xmotion-project/karaloop/src/karaloopP1_0.gif

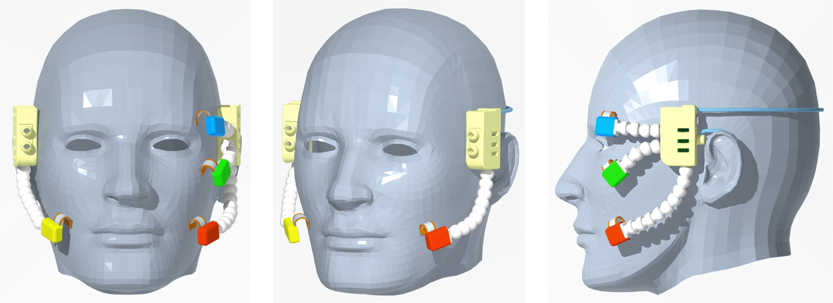
src/karaloopP1_0.gif
