xmotion-project/karaloop/src/karaloopP1_0_photo.gif

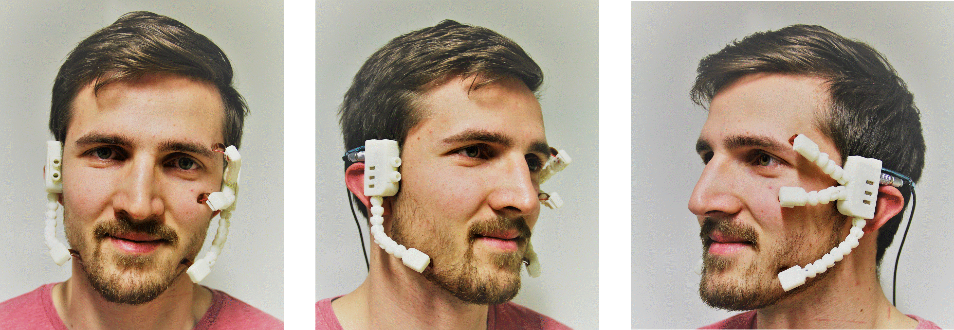
src/karaloopP1_0_photo.gif
