xmotion-project/karaloop/src/karaloopP2_0.gif

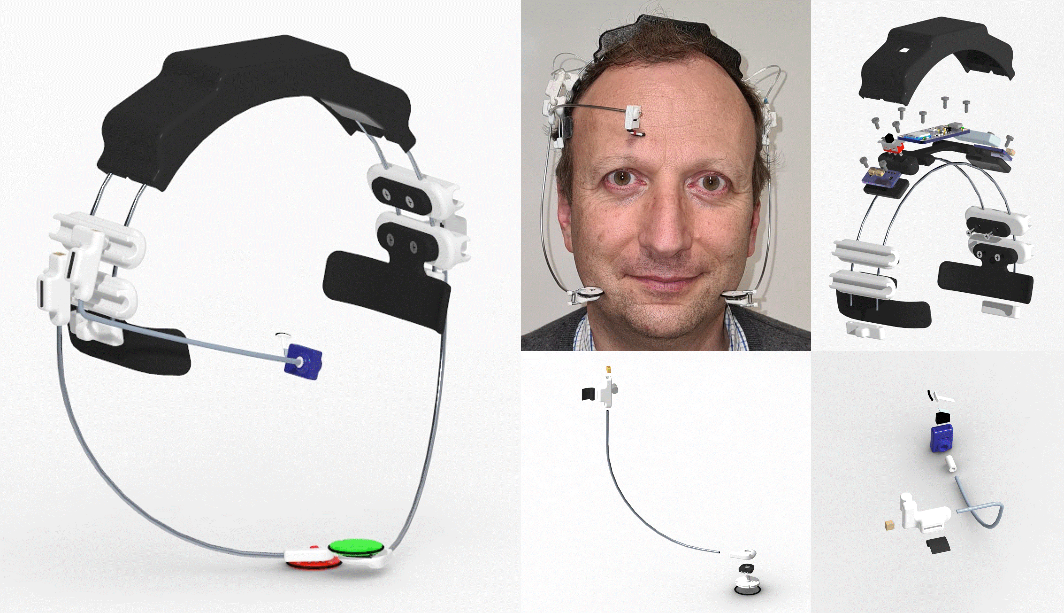
src/karaloopP2_0.gif
