xmotion-project/karaloop/src/karaloopP3_0.gif

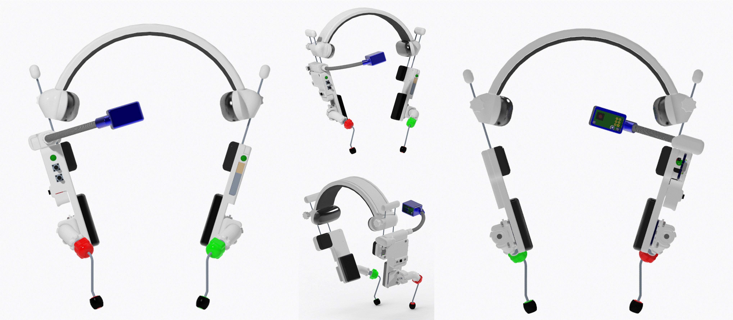
src/karaloopP3_0.gif
