xmotion-project/karaloop/src/ShortDemo_iMacWhatsapp.gif

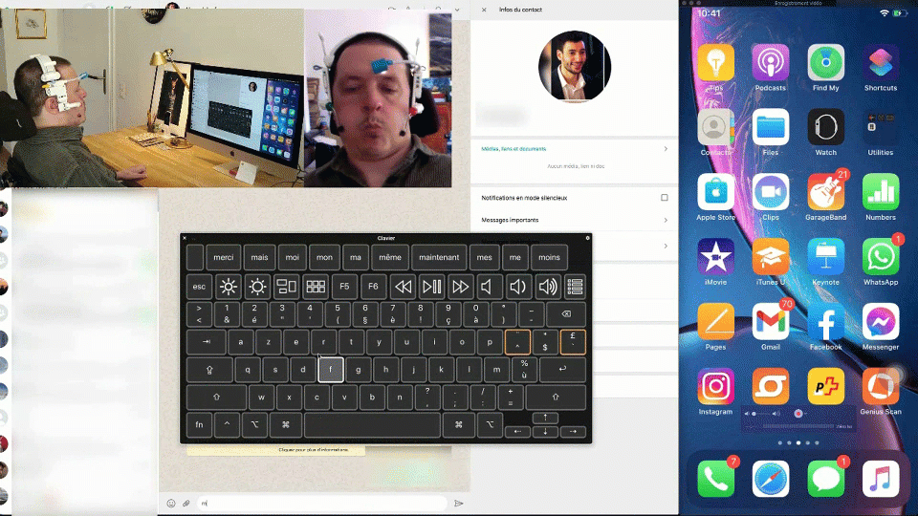
src/ShortDemo_iMacWhatsapp.gif
