xmotion-project/karaloop/src/karaloopP1_0_components.jpg

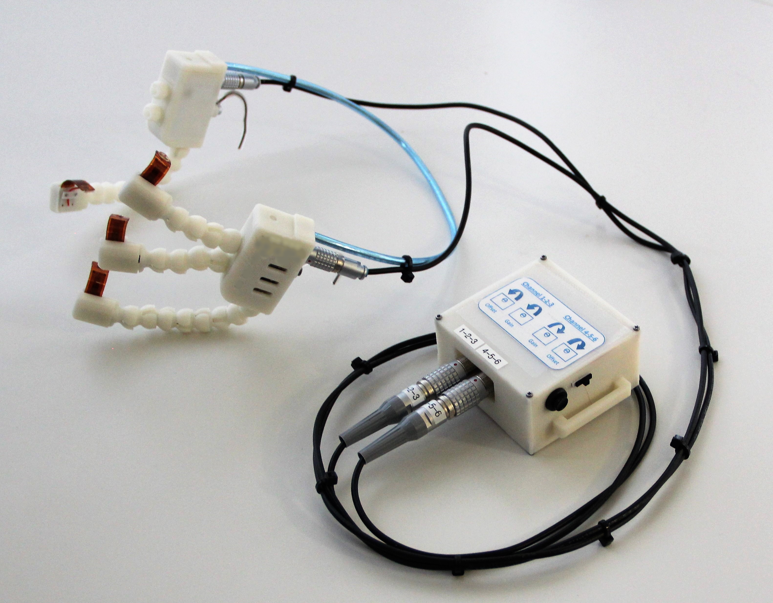
src/karaloopP1_0_components.jpg
