xmotion-project/karaloop/src/karaloopP1_0_parts.gif

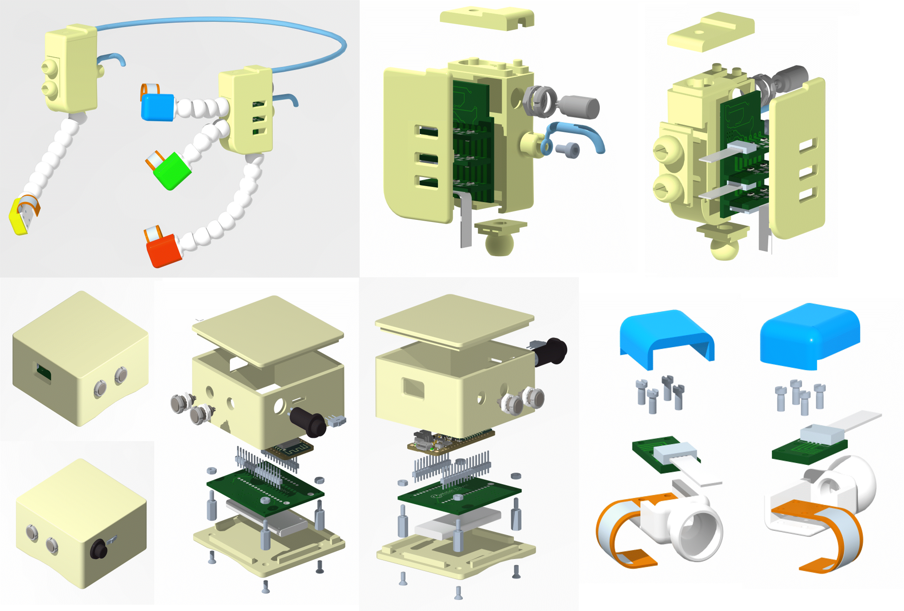
src/karaloopP1_0_parts.gif
