xmotion-project/karaloop/karaloop_P3_0/Hardware/Mechanical Design/Sub-assembly/Optical probe/STL/sliding_join_female.stl

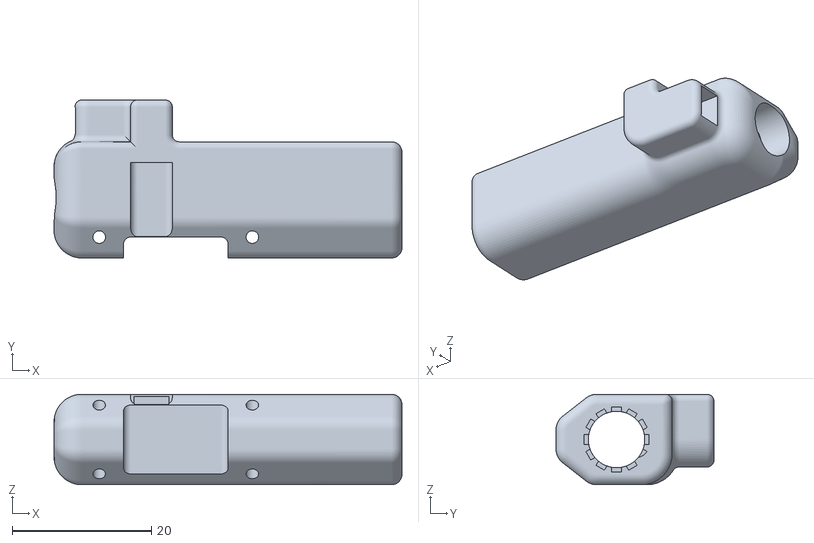
[picture p31: CAD file, 2021-08-26]
karaloop_P3_0/Hardware/Mechanical Design/Sub-assembly/Optical probe/STL/sliding_join_female.stl
50.0 x 22.7 x 13.0
