xmotion-project/karaloop/karaloop_P3_0/Hardware/Mechanical Design/Sub-assembly/Right hub/STL/hub_end_part.stl

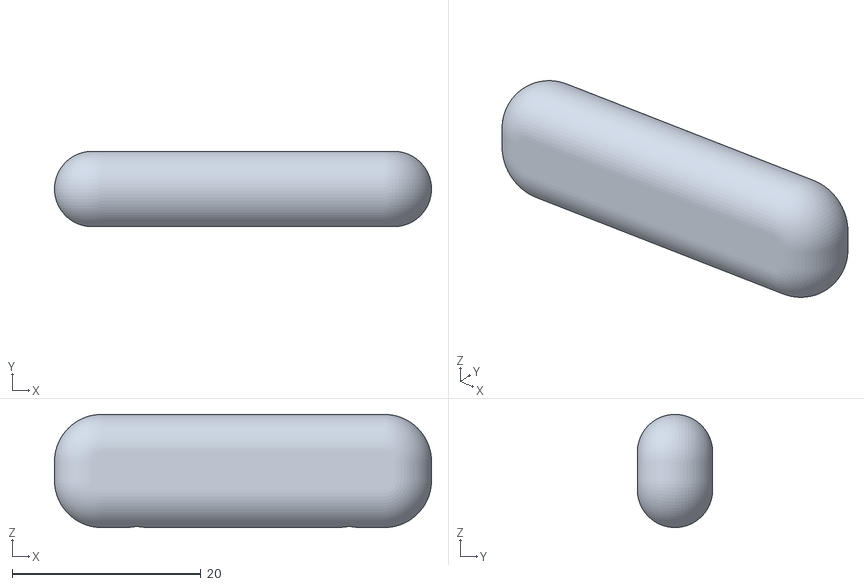
[picture p32: CAD file, 2021-08-26]
karaloop_P3_0/Hardware/Mechanical Design/Sub-assembly/Right hub/STL/hub_end_part.stl
40.0 x 8.00 x 12.0
