xmotion-project/karaloop/karaloop_P1_0/Hardware/Mechanical Design/STL/bottom_cover_control_box.stl

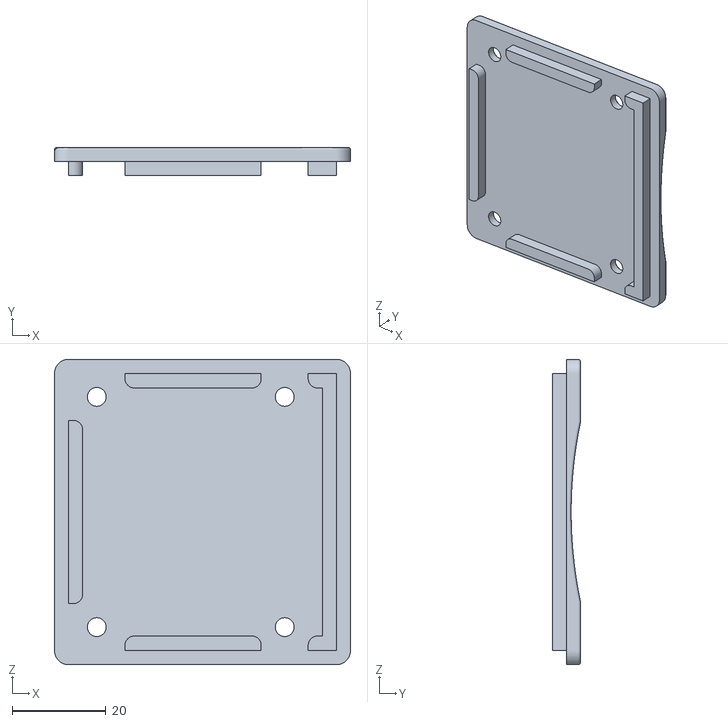
[picture p33: CAD file, 2022-07-11]
karaloop_P1_0/Hardware/Mechanical Design/STL/bottom_cover_control_box.stl
63.0 x 6.00 x 65.0
