xmotion-project/karaloop/karaloop_P2_0/Hardware/Mechanical Design/Sub-assembly/Headset band/STL/bottom_flex_side_pad.stl

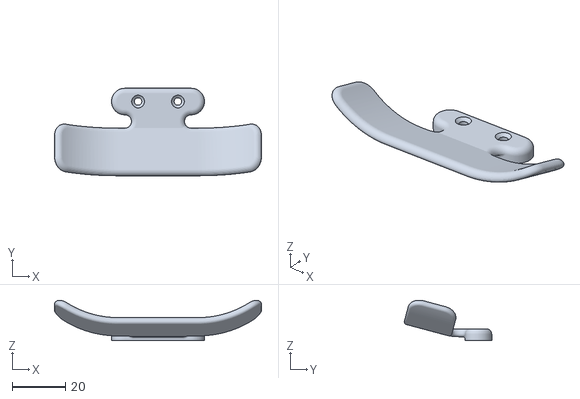
[picture p34: CAD file, 2021-08-26]
karaloop_P2_0/Hardware/Mechanical Design/Sub-assembly/Headset band/STL/bottom_flex_side_pad.stl
77.9 x 32.9 x 15.2
