xmotion-project/karaloop/karaloop_P2_0/Hardware/Mechanical Design/Sub-assembly/Potentiometric probes/STL/potentiometer_holder.stl

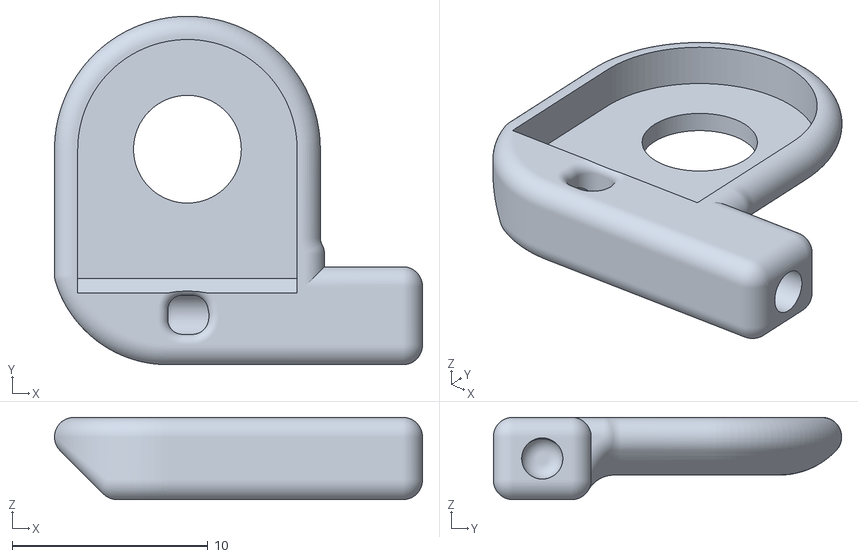
[picture p35: CAD file, 2021-08-26]
karaloop_P2_0/Hardware/Mechanical Design/Sub-assembly/Potentiometric probes/STL/potentiometer_holder.stl
18.8 x 17.8 x 4.20
