xmotion-project/karaloop/karaloop_P2_0/Hardware/Mechanical Design/Sub-assembly/Switch probe/STL/switch_lever_arm.stl

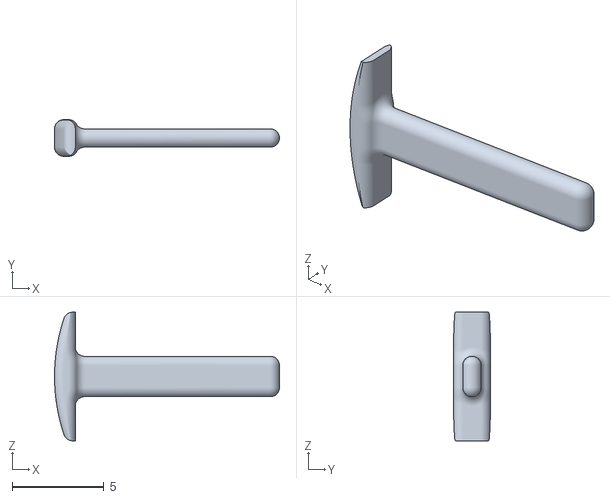
[picture p36: CAD file, 2021-08-26]
karaloop_P2_0/Hardware/Mechanical Design/Sub-assembly/Switch probe/STL/switch_lever_arm.stl
12.2 x 2.00 x 7.00
