xmotion-project/karaloop/karaloop_P3_0/Hardware/Mechanical Design/Sub-assembly/Headset band/STL/locking_wheel.stl

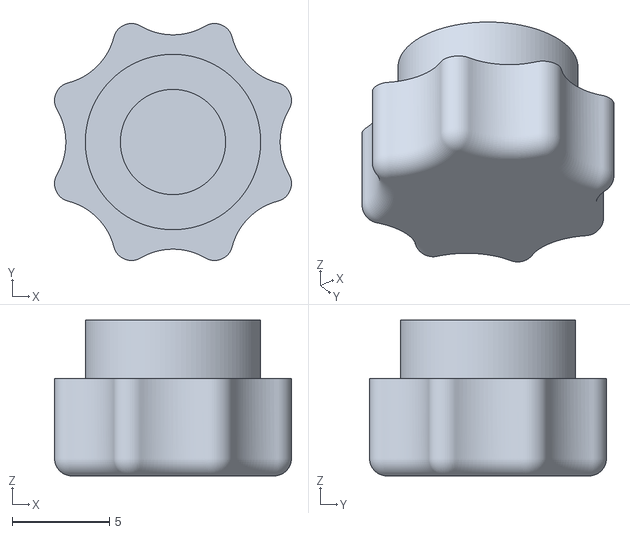
[picture p37: CAD file, 2021-08-26]
karaloop_P3_0/Hardware/Mechanical Design/Sub-assembly/Headset band/STL/locking_wheel.stl
12.2 x 12.2 x 8.00
