xmotion-project/karaloop/karaloop_P3_0/Hardware/Mechanical Design/Sub-assembly/Magnetic probe/STL/magnetometer_top_cover.stl

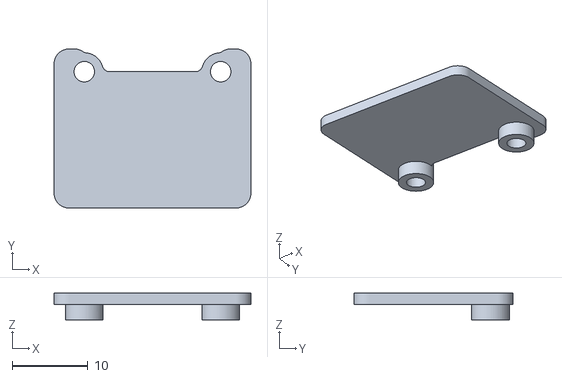
[picture p38: CAD file, 2021-08-26]
karaloop_P3_0/Hardware/Mechanical Design/Sub-assembly/Magnetic probe/STL/magnetometer_top_cover.stl
26.0 x 21.0 x 3.50
