xmotion-project/karaloop/karaloop_P3_0/Hardware/Mechanical Design/Sub-assembly/Optical probe/STL/wires_cover.stl

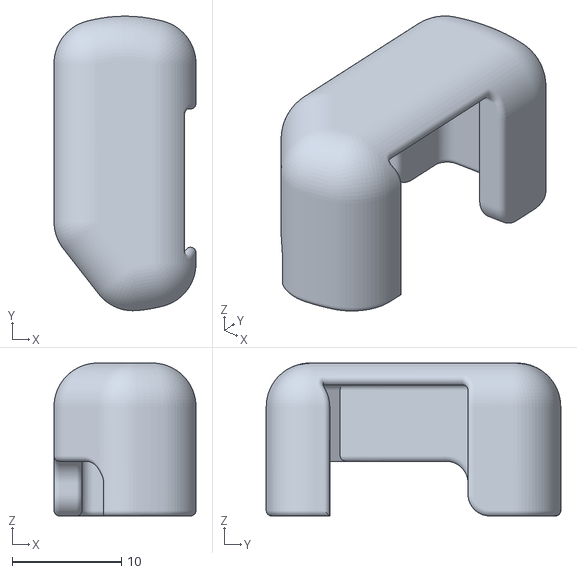
[picture p39: CAD file, 2021-08-26]
karaloop_P3_0/Hardware/Mechanical Design/Sub-assembly/Optical probe/STL/wires_cover.stl
13.0 x 27.0 x 14.0
