xmotion-project/karaloop/karaloop_P3_0/Hardware/Mechanical Design/Sub-assembly/Right hub/STL/right_hub_holder.stl

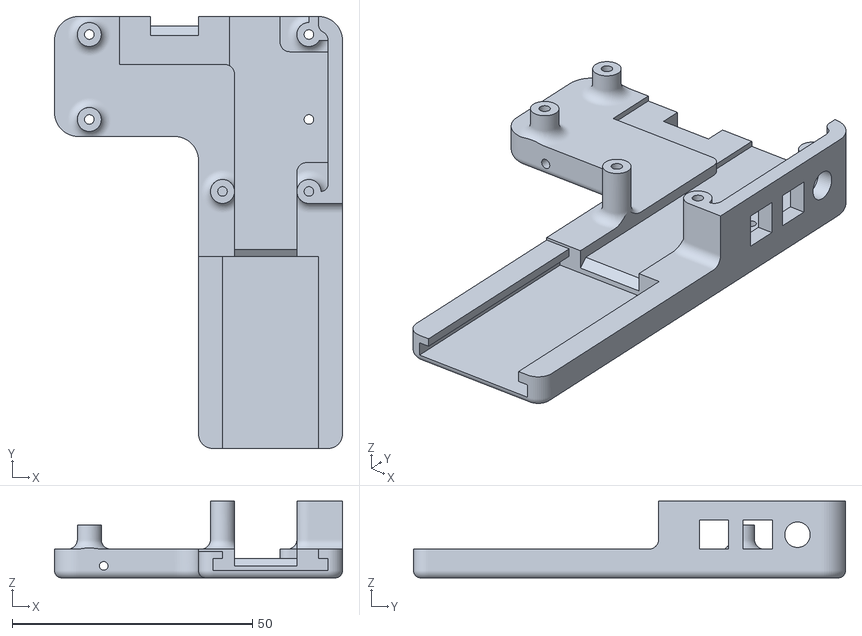
[picture p40: CAD file, 2021-08-26]
karaloop_P3_0/Hardware/Mechanical Design/Sub-assembly/Right hub/STL/right_hub_holder.stl
60.0 x 90.0 x 16.0
