xmotion-project/karaloop/karaloop_P1_0/Hardware/Mechanical Design/STL/middle_control_box.stl

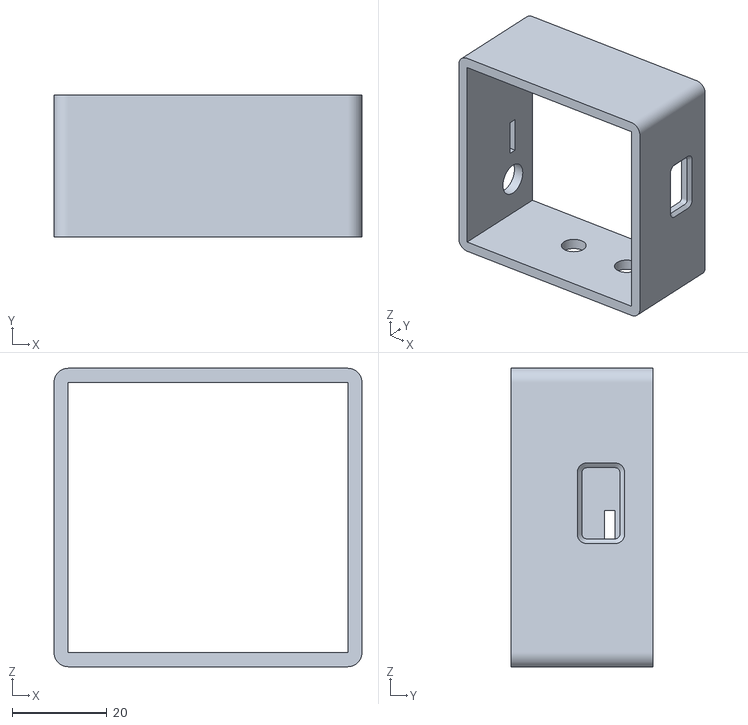
[picture p41: CAD file, 2022-07-11]
karaloop_P1_0/Hardware/Mechanical Design/STL/middle_control_box.stl
65.0 x 30.0 x 63.0
