xmotion-project/karaloop/karaloop_P2_0/Hardware/Mechanical Design/Sub-assembly/Headset band/STL/pcb_conn_holder.stl

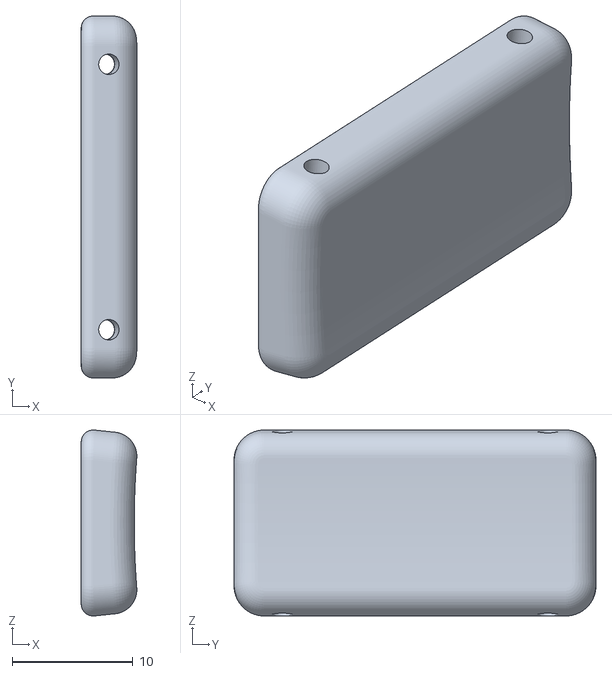
[picture p42: CAD file, 2021-08-26]
karaloop_P2_0/Hardware/Mechanical Design/Sub-assembly/Headset band/STL/pcb_conn_holder.stl
4.61 x 30.0 x 15.4
