xmotion-project/karaloop/karaloop_P2_0/Hardware/Mechanical Design/Sub-assembly/Potentiometric probes/STL/potentiometric_probe_holder_l.stl

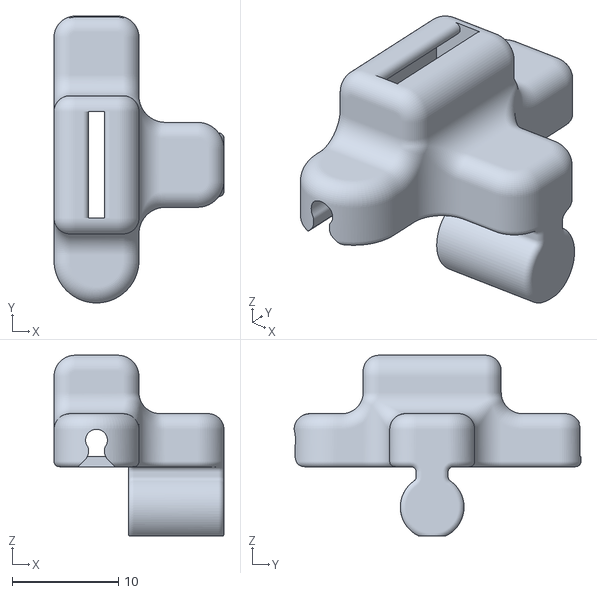
[picture p43: CAD file, 2021-08-26]
karaloop_P2_0/Hardware/Mechanical Design/Sub-assembly/Potentiometric probes/STL/potentiometric_probe_holder_l.stl
16.0 x 27.0 x 17.0
