xmotion-project/karaloop/karaloop_P2_0/Hardware/Mechanical Design/Sub-assembly/Switch probe/STL/switch_probe_holder.stl

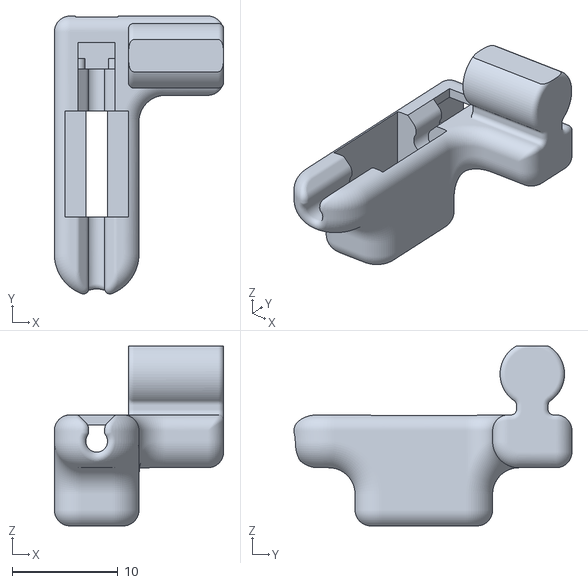
[picture p44: CAD file, 2021-08-26]
karaloop_P2_0/Hardware/Mechanical Design/Sub-assembly/Switch probe/STL/switch_probe_holder.stl
16.0 x 26.3 x 17.0
