xmotion-project/karaloop/karaloop_P3_0/Hardware/Mechanical Design/Sub-assembly/Headset band/STL/flexible_headband.stl

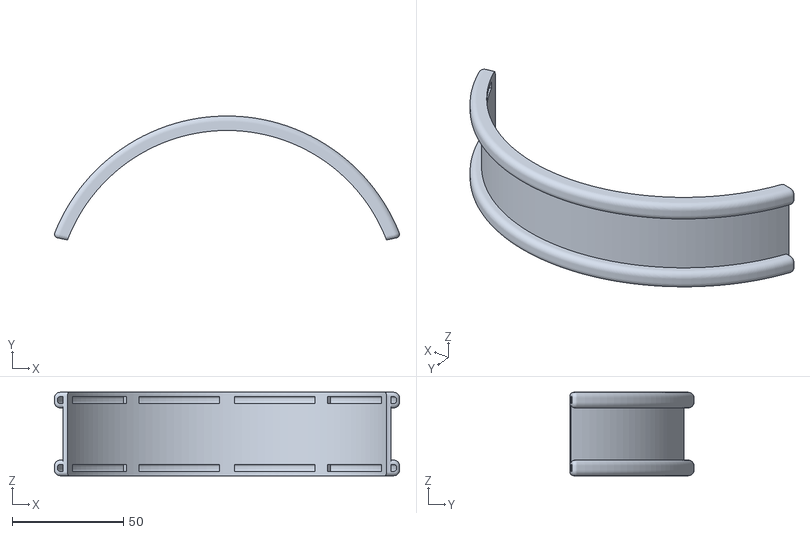
[picture p45: CAD file, 2021-08-26]
karaloop_P3_0/Hardware/Mechanical Design/Sub-assembly/Headset band/STL/flexible_headband.stl
154.9 x 55.7 x 37.5
