xmotion-project/karaloop/karaloop_P3_0/Hardware/Mechanical Design/Sub-assembly/Magnetic probe/STL/spring_holder_part1.stl

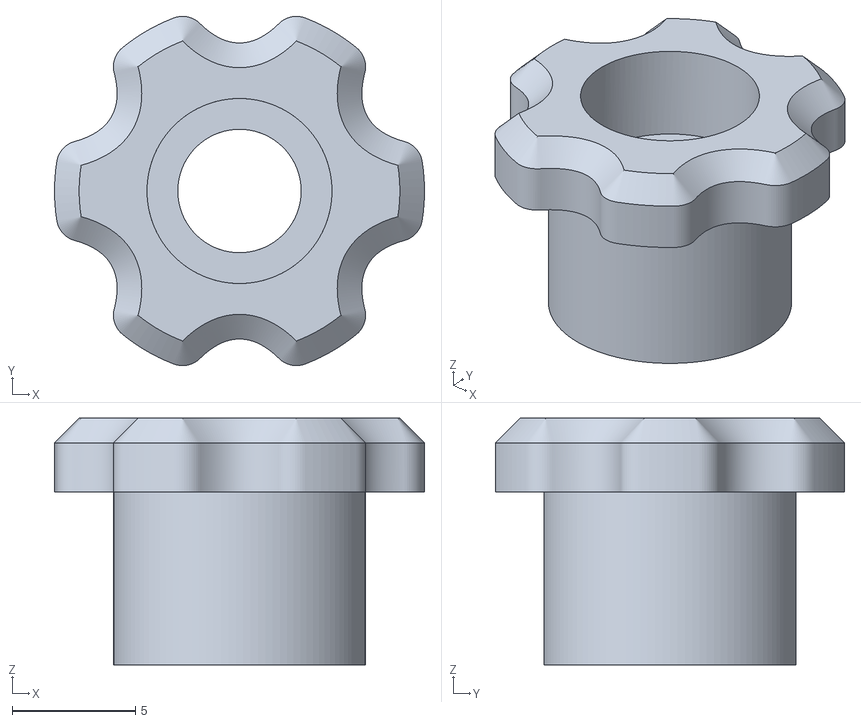
[picture p46: CAD file, 2021-08-26]
karaloop_P3_0/Hardware/Mechanical Design/Sub-assembly/Magnetic probe/STL/spring_holder_part1.stl
15.0 x 14.2 x 10.0
