xmotion-project/karaloop/karaloop_P3_0/Hardware/Mechanical Design/Sub-assembly/Optical probe/STL/sliding_join_male.stl

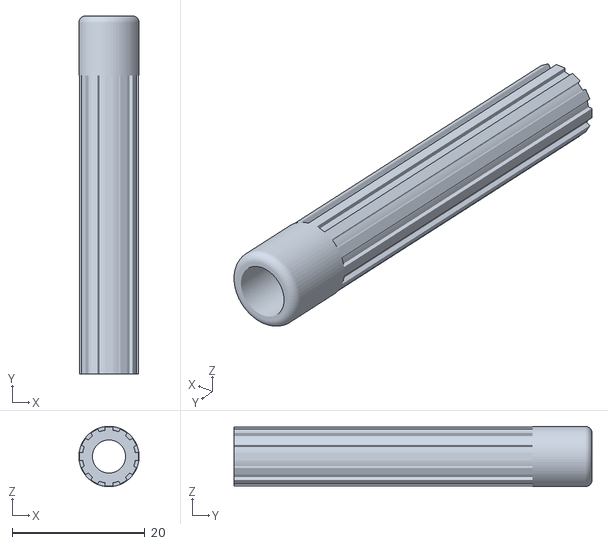
[picture p47: CAD file, 2021-08-26]
karaloop_P3_0/Hardware/Mechanical Design/Sub-assembly/Optical probe/STL/sliding_join_male.stl
9.10 x 54.0 x 9.09
