xmotion-project/karaloop/karaloop_P1_0/Hardware/Mechanical Design/STL/top_cover_control_box.stl

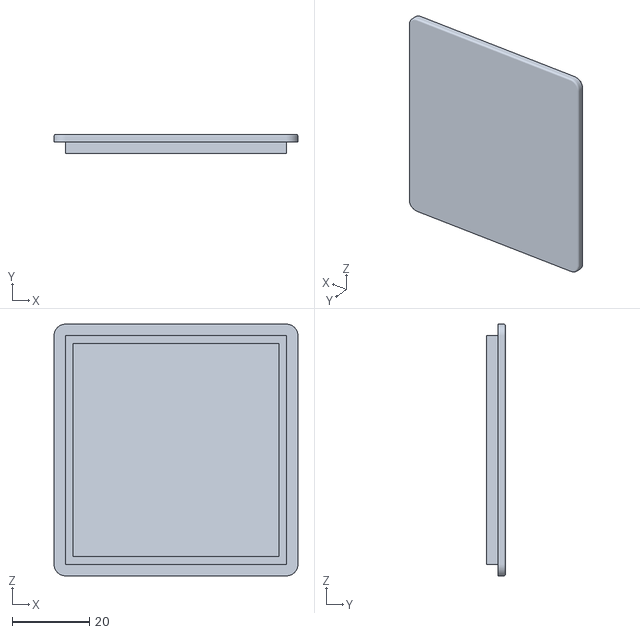
[picture p48: CAD file, 2022-07-11]
karaloop_P1_0/Hardware/Mechanical Design/STL/top_cover_control_box.stl
63.0 x 5.00 x 65.0
