xmotion-project/karaloop/karaloop_P2_0/Hardware/Mechanical Design/Sub-assembly/Headset band/STL/bluefruit_holder.stl

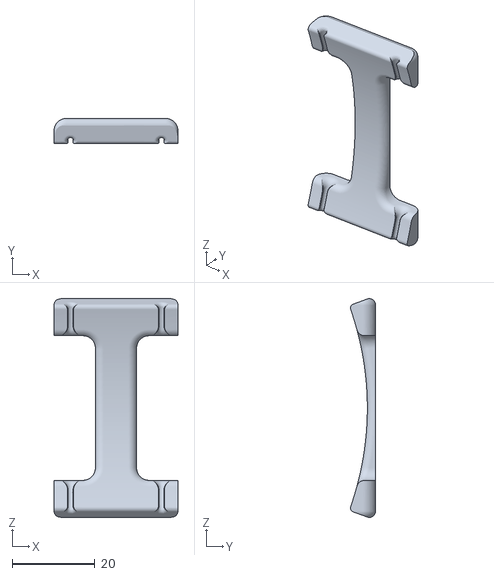
[picture p49: CAD file, 2021-08-26]
karaloop_P2_0/Hardware/Mechanical Design/Sub-assembly/Headset band/STL/bluefruit_holder.stl
30.0 x 6.10 x 53.0
