xmotion-project/karaloop/karaloop_P2_0/Hardware/Mechanical Design/Sub-assembly/Switch probe/STL/switch_housing.stl

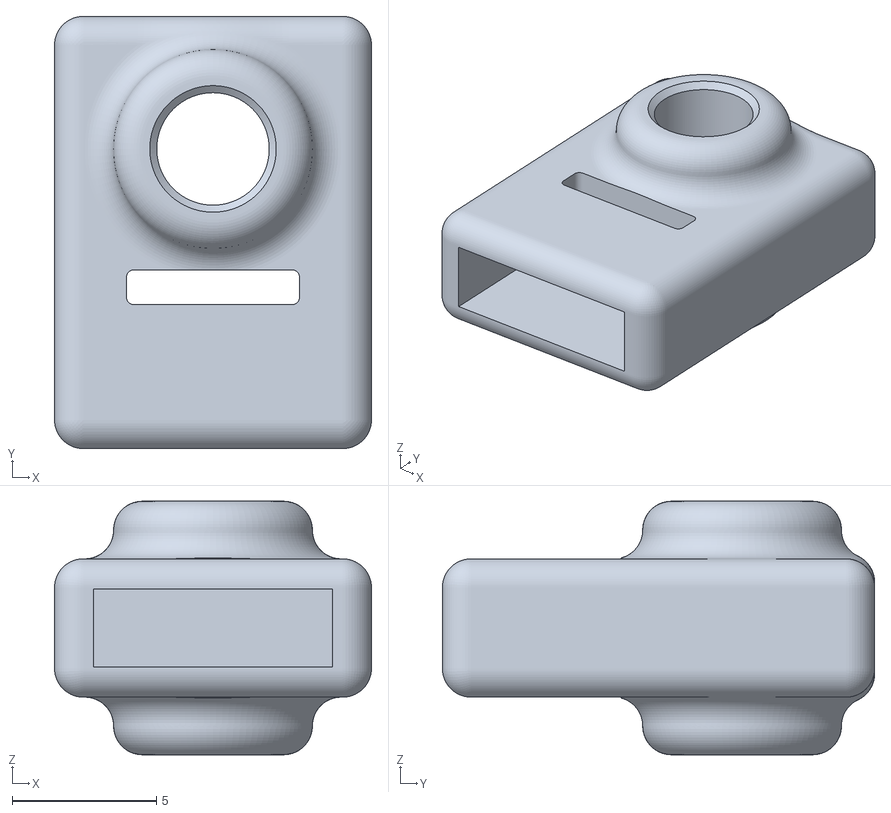
[picture p50: CAD file, 2021-08-26]
karaloop_P2_0/Hardware/Mechanical Design/Sub-assembly/Switch probe/STL/switch_housing.stl
11.0 x 15.0 x 8.80
