xmotion-project/karaloop/karaloop_P3_0/Hardware/Mechanical Design/Sub-assembly/Headset band/STL/flexible_top_cover.stl

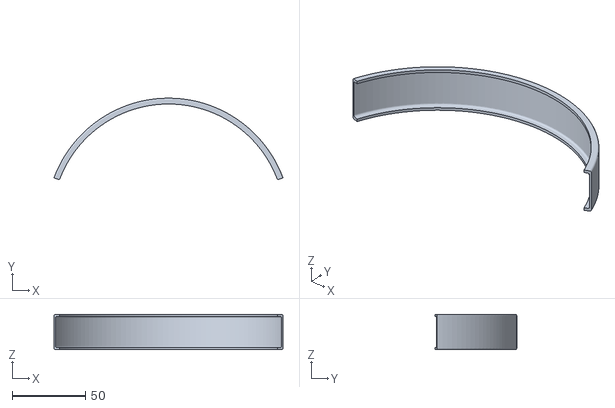
[picture p51: CAD file, 2021-08-26]
karaloop_P3_0/Hardware/Mechanical Design/Sub-assembly/Headset band/STL/flexible_top_cover.stl
156.1 x 55.7 x 24.0
