xmotion-project/karaloop/karaloop_P3_0/Hardware/Mechanical Design/Sub-assembly/Magnetic probe/STL/spring_holder_part2.stl

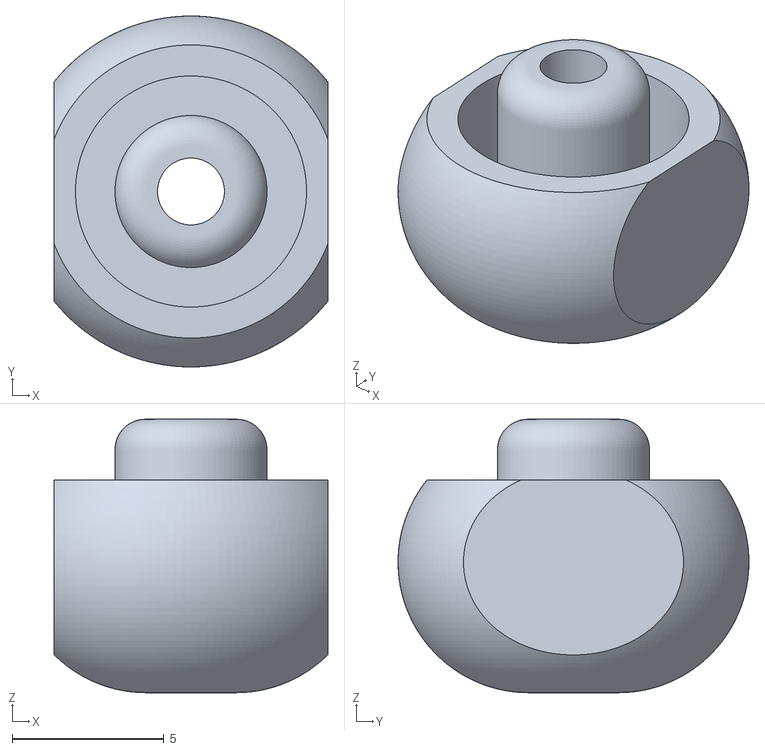
[picture p52: CAD file, 2021-08-26]
karaloop_P3_0/Hardware/Mechanical Design/Sub-assembly/Magnetic probe/STL/spring_holder_part2.stl
9.00 x 11.5 x 9.00
