xmotion-project/karaloop/karaloop_P1_0/Hardware/Mechanical Design/STL/ball_joint_connector_12.stl

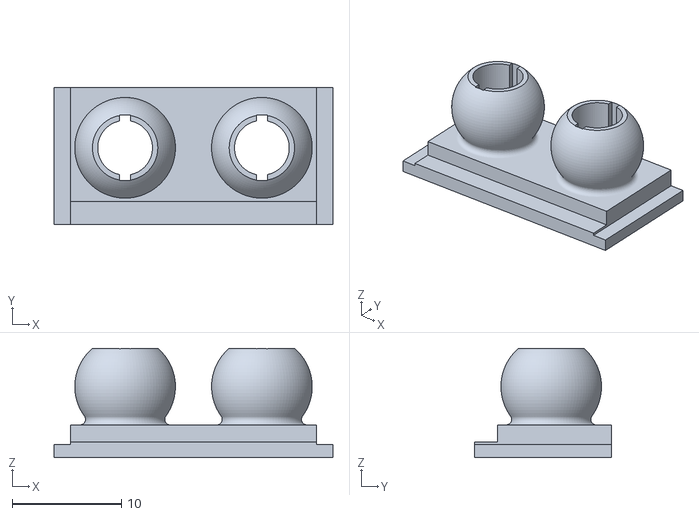
[picture p53: CAD file, 2021-08-26]
karaloop_P1_0/Hardware/Mechanical Design/STL/ball_joint_connector_12.stl
25.5 x 12.5 x 10.0
