xmotion-project/karaloop/karaloop_P2_0/Hardware/Mechanical Design/Sub-assembly/Headset band/STL/switch_holder.stl

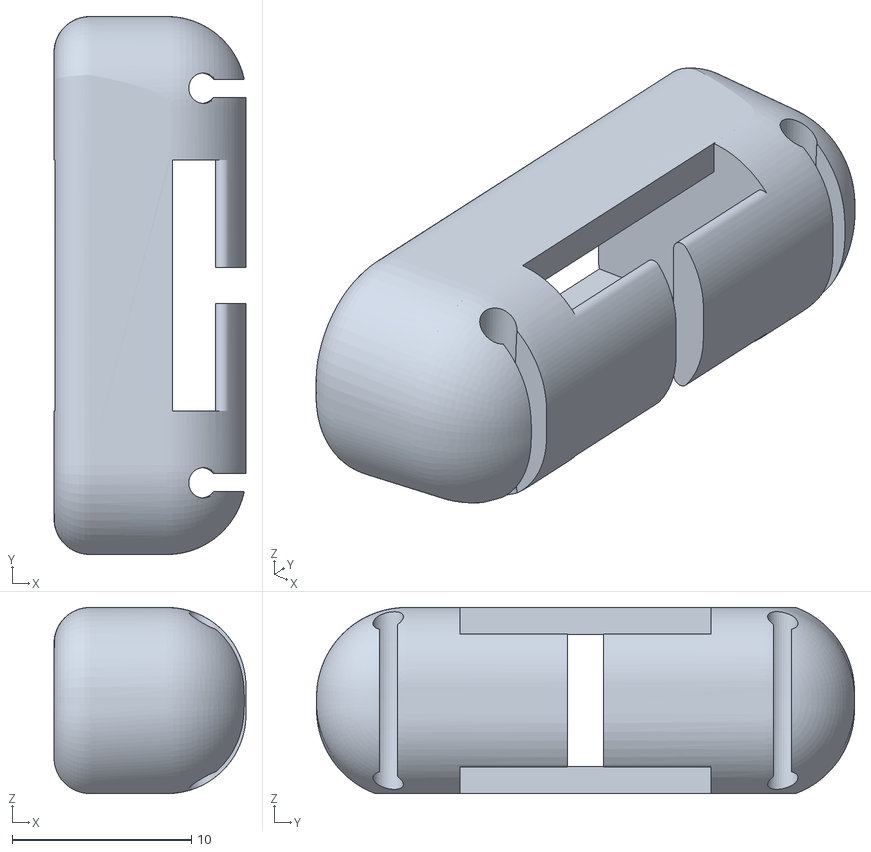
[picture p54: CAD file, 2021-08-26]
karaloop_P2_0/Hardware/Mechanical Design/Sub-assembly/Headset band/STL/switch_holder.stl
10.7 x 30.0 x 10.4
