xmotion-project/karaloop/karaloop_P3_0/Hardware/Mechanical Design/Sub-assembly/Magnetic probe/STL/right_tube.stl

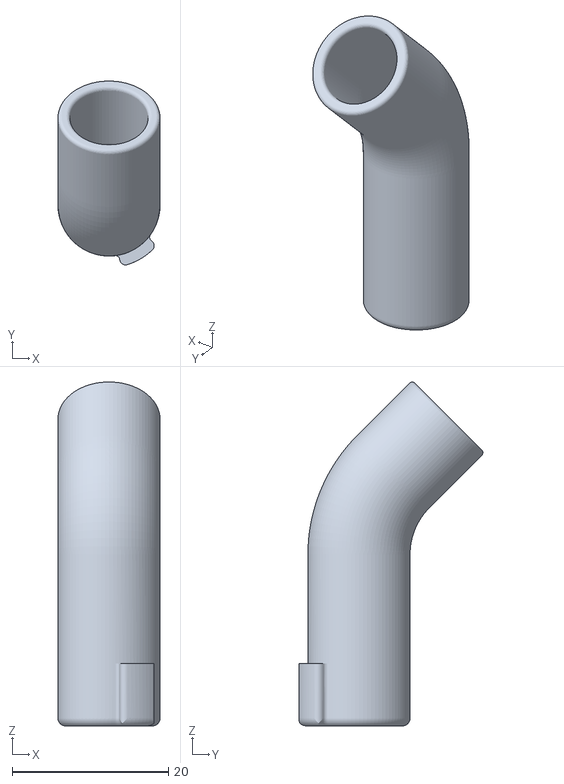
[picture p55: CAD file, 2021-08-26]
karaloop_P3_0/Hardware/Mechanical Design/Sub-assembly/Magnetic probe/STL/right_tube.stl
13.1 x 23.6 x 44.1
