xmotion-project/karaloop/karaloop_P1_0/Hardware/Mechanical Design/STL/ball_joints_right.stl

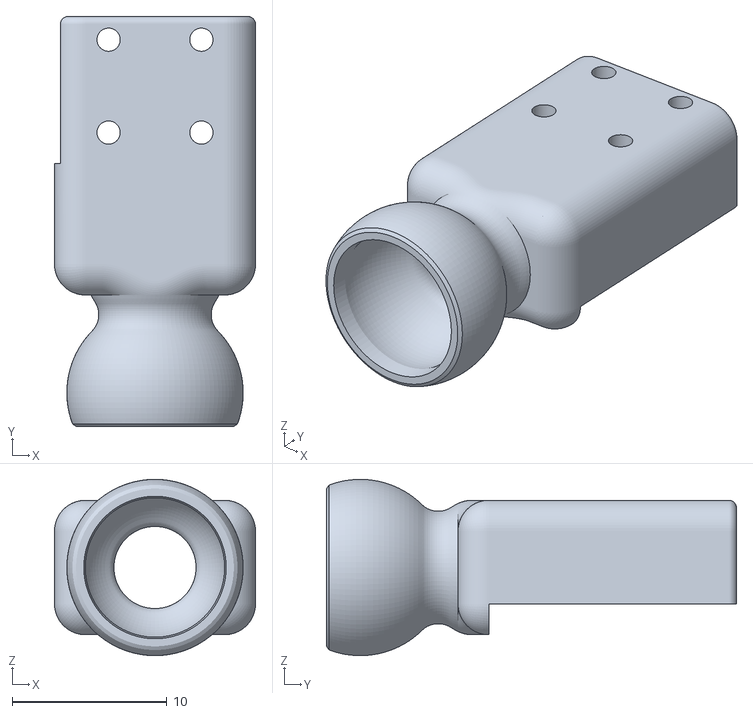
[picture p56: CAD file, 2021-08-26]
karaloop_P1_0/Hardware/Mechanical Design/STL/ball_joints_right.stl
13.0 x 26.5 x 11.4
