xmotion-project/karaloop/karaloop_P2_0/Hardware/Mechanical Design/Sub-assembly/Headset band/STL/end_part_headband.stl

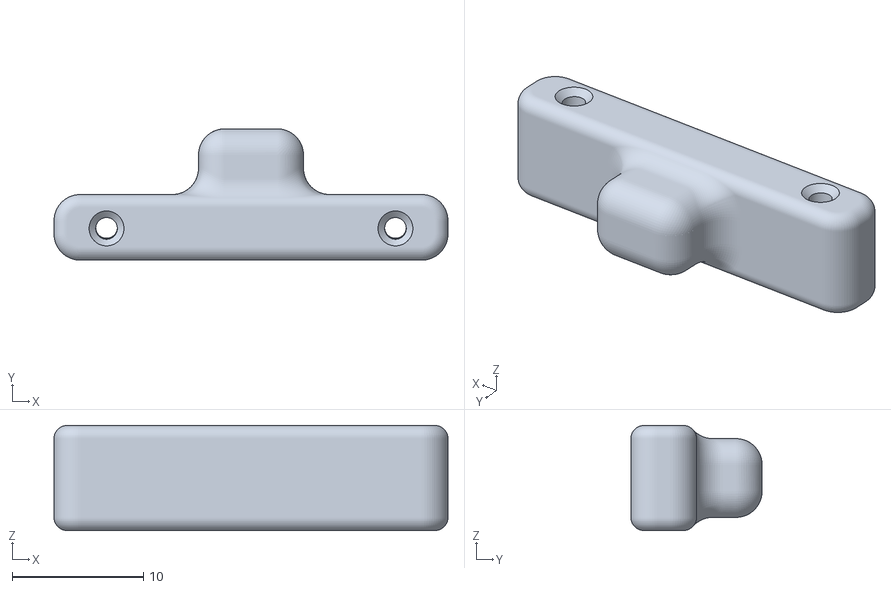
[picture p57: CAD file, 2021-08-26]
karaloop_P2_0/Hardware/Mechanical Design/Sub-assembly/Headset band/STL/end_part_headband.stl
30.0 x 10.0 x 8.00
