xmotion-project/karaloop/karaloop_P1_0/Hardware/Mechanical Design/STL/ball_joint_connector_3.stl

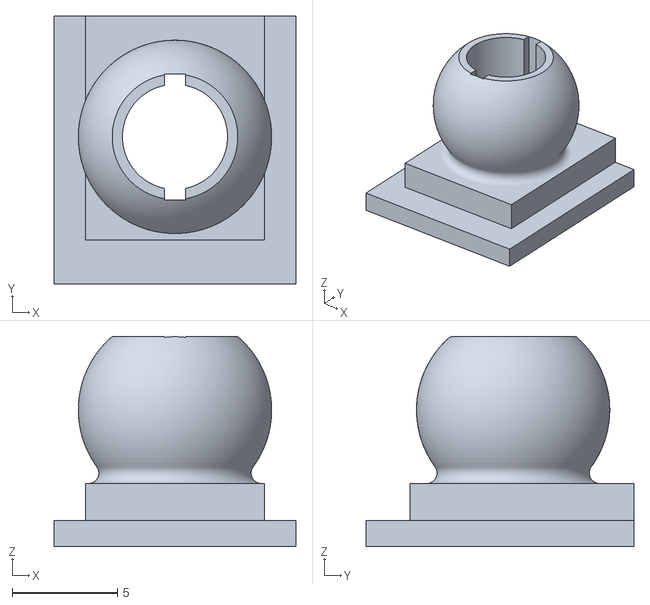
[picture p58: CAD file, 2021-08-26]
karaloop_P1_0/Hardware/Mechanical Design/STL/ball_joint_connector_3.stl
11.5 x 12.8 x 10.0
