xmotion-project/karaloop/karaloop_P3_0/Hardware/Mechanical Design/Sub-assembly/Magnetic probe/STL/spherical_socket.stl

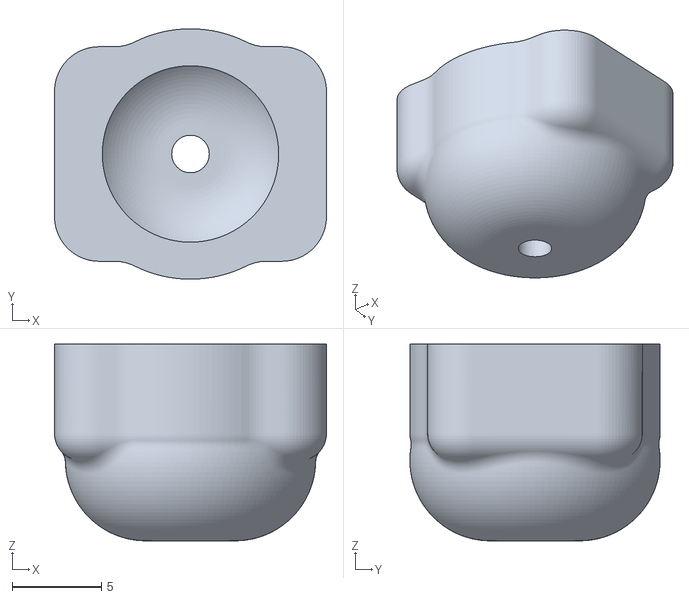
[picture p60: CAD file, 2021-08-26]
karaloop_P3_0/Hardware/Mechanical Design/Sub-assembly/Magnetic probe/STL/spherical_socket.stl
15.2 x 14.0 x 11.0
