xmotion-project/karaloop/karaloop_P1_0/Hardware/Mechanical Design/STL/ball_joints.stl

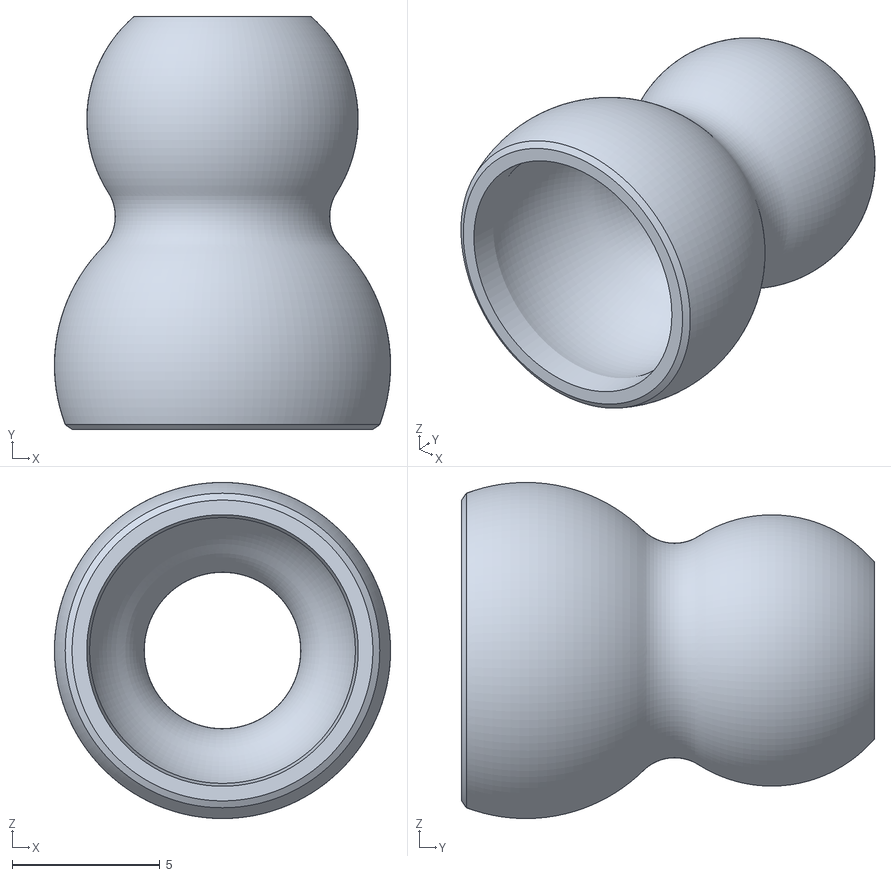
[picture p61: CAD file, 2021-08-26]
karaloop_P1_0/Hardware/Mechanical Design/STL/ball_joints.stl
11.4 x 14.0 x 11.4
