xmotion-project/karaloop/karaloop_P1_0/Hardware/Mechanical Design/STL/hub_box_right.stl

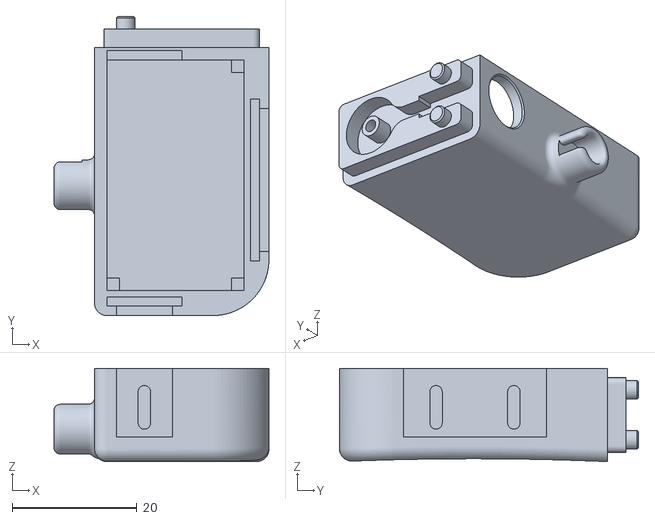
[picture p64: CAD file, 2021-08-26]
karaloop_P1_0/Hardware/Mechanical Design/STL/hub_box_right.stl
34.5 x 48.0 x 15.0
