xmotion-project/karaloop/karaloop_P1_0/Hardware/Mechanical Design/STL/protective_cover_probe_right.stl

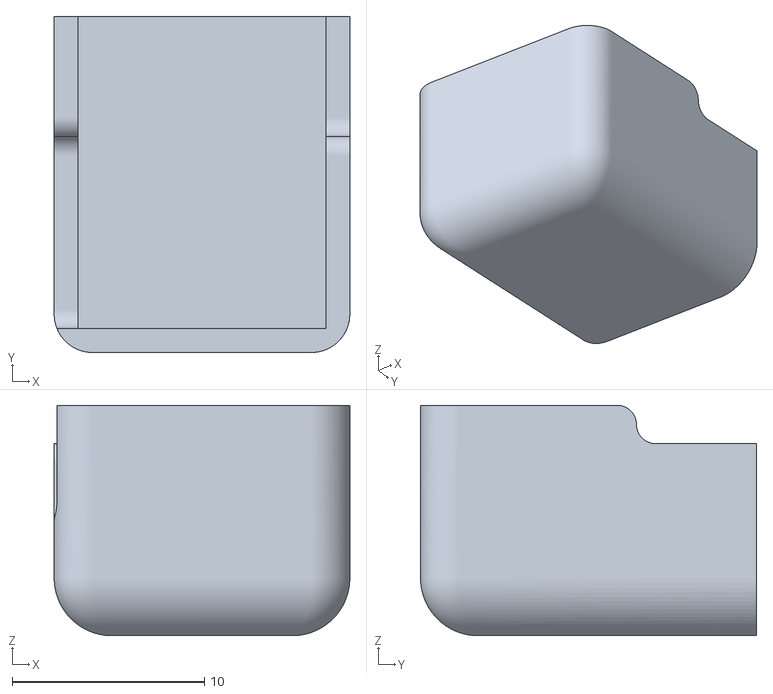
[picture p65: CAD file, 2021-08-26]
karaloop_P1_0/Hardware/Mechanical Design/STL/protective_cover_probe_right.stl
15.4 x 17.5 x 12.0
