xmotion-project/karaloop/karaloop_P1_0/Hardware/Mechanical Design/STL/hub_support_cover_right.stl

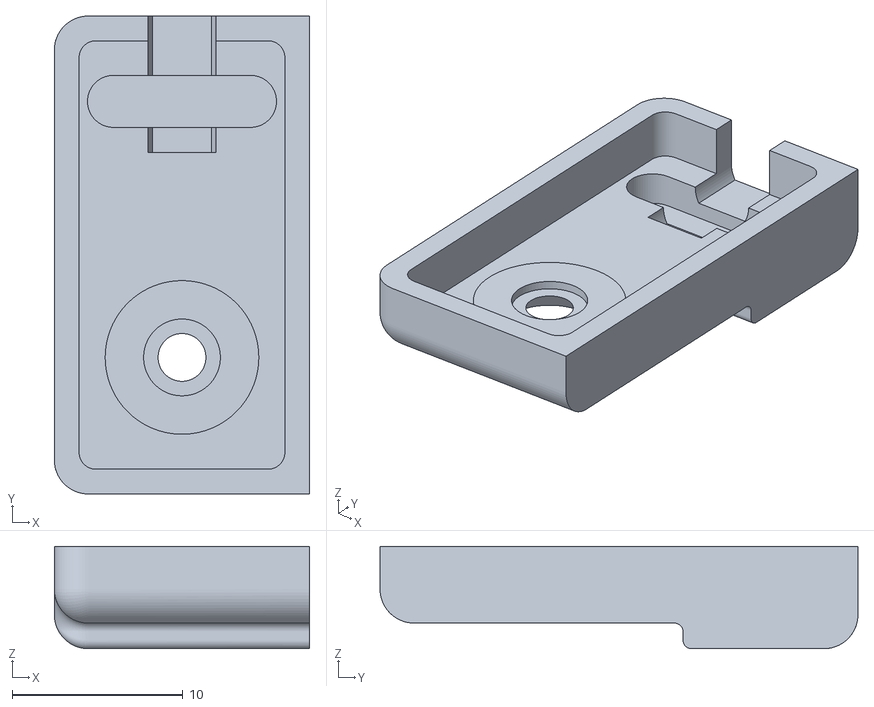
[picture p66: CAD file, 2021-08-26]
karaloop_P1_0/Hardware/Mechanical Design/STL/hub_support_cover_right.stl
15.0 x 28.0 x 6.00
