xmotion-project/karaloop/karaloop_P1_0/Hardware/Mechanical Design/STL/hub_support_cover_left.stl

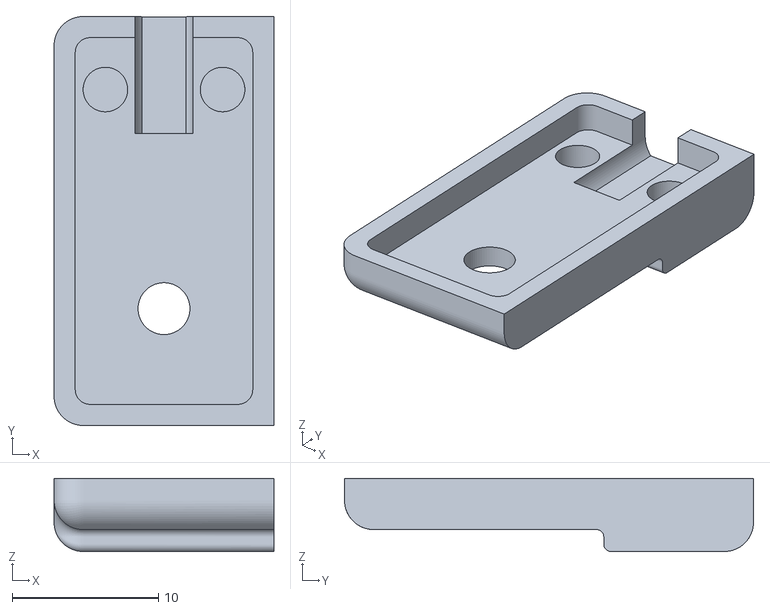
[picture p67: CAD file, 2021-08-26]
karaloop_P1_0/Hardware/Mechanical Design/STL/hub_support_cover_left.stl
15.1 x 28.0 x 5.00
